Canterrain/bread-proof-monitor/proof_state.cpp

#include "proof_state.h"

#include <math.h>

#include "outcome_feedback.h"
#include "recipe_presets.h"

namespace {
constexpr int8_t kNoEventIndex = -1;
constexpr unsigned long kDistanceStaleAfterMs = 15000;
// A single noisy sample shouldn't permanently raise the floor: require the reading to stay
// above the current peak for a few consecutive ticks before it's trusted. This is short
// enough to accept genuine rise (which persists for many minutes, not seconds) but long
// enough to reject a one-off VL53L0X jitter spike, which reverts within a tick or two.
constexpr unsigned long kPeakConfirmMs = 8000;
// 8s is long enough to reject noise on a tall dough (a few mm of jitter is a small percentage of
// the height), but not on a very shallow one - Detroit Pizza's ~10mm-tall pan-pressed Final stage
// let ~2mm of ordinary jitter hold for a full 8s and lock in a false 15% peak (2026-09-29 live
// bake). Real rise is persistent (keeps climbing over minutes); noise is transient (reverts) -
// so a shallow dough needs a much longer hold before a candidate peak is trusted. This scales
// linearly between kPeakConfirmMs (at/above kTallConfirmReferenceHeightMm, unchanged from before)
// and kMaxPeakConfirmMs (at/below kShallowConfirmReferenceHeightMm) - see peakConfirmMs(). The
// exact numbers are a first-pass estimate from 2026-09-30 repeatability data (glass ~1mm spread
// vs. metal pans ~3mm spread on Set Empty captures, same order of magnitude as the phantom peak),
// not yet validated against a live shallow bake's actual noise *timing* - tune against the next
// one (see the pan-empty-calibration-test memory).
constexpr unsigned long kMaxPeakConfirmMs = 90000;
constexpr float kTallConfirmReferenceHeightMm = 60.0f;
constexpr float kShallowConfirmReferenceHeightMm = 15.0f;
// "Rise has slowed" message: the confirmed peak has to gain kStallMinGainPercent within
// kStallWindowMs, or the monitor says so - unless a fold or the target is already within
// kStallNearMilestonePercent (it is about to fire anyway). Measurement-based, not a timer: the
// window only measures how fast the dough is moving. First-guess numbers from the 2026-10-06
// no-knead bake (a cold-kitchen dough sat flat for about an hour with nothing to say so); tune
// against real runs.
constexpr unsigned long kStallWindowMs = 30UL * 60UL * 1000UL;
constexpr float kStallMinGainPercent = 2.0f;
constexpr float kStallNearMilestonePercent = 3.0f;
constexpr unsigned long kDefaultReferenceFloorSeconds = 20 * 60;
constexpr unsigned long kMinSegmentFloorSeconds = 8 * 60;
constexpr unsigned long kMaxSegmentFloorSeconds = 40 * 60;
// How long after Set Starting Dough Height, or after completing a fold, the rise is held steady
// (at 0% for a fresh start, at the already-earned percentage after a fold). Smoothing the surface and
// then watching it relax back up (or the mount shifting after being handled) moves the reading
// several mm in the first minutes, which would otherwise be counted - and permanently locked
// in by the peak - as real rise. Once the window ends, the settled reading becomes the start.
constexpr unsigned long kSettleWindowSeconds = 10 * 60;
// A fold or manual re-baseline only briefly disturbs a surface that's already mid-rise, unlike a
// fresh start where nothing has settled yet - real fold-to-fold gaps (King Arthur's own no-knead
// schedule runs ~15 minutes apart) leave little room for a full 10-minute hold on top of them.
constexpr unsigned long kPostDisturbanceSettleSeconds = 3 * 60;
// The peak only ever moves up, and this sensor jitters a few mm at the rig's standoff (about 1.4%
// of rise per mm on a 70mm dough), so symmetric noise alone turns into a one-sided climb in the
// peak within minutes. A new peak has to clear the old one by more than this to count.
constexpr float kPeakDeadbandMm = 3.0f;
// A fixed mm deadband is a small margin on a tall dough but can swallow most of a shallow
// container's whole target - 3mm was about 4% of a 70mm no-knead bucket but 8%+ of a ~36mm
// Detroit Pizza bulk container, against a 10% fold trigger. Capped here so a shallow container
// can't lose most of its own trigger range to noise margin; tall doughs are unaffected as long
// as the mm-based value stays under this.
constexpr float kMaxPeakDeadbandPercent = 4.0f;
constexpr float kReferenceTempF = 75.0f;
constexpr float kFermentationDoublingSpanF = 18.0f;

bool riseInputsReady(const AppState& state) {
  return proofHasEmptyCalibration(state) && proofHasStartingHeight(state) && state.smoothedDistanceMm > 0.0f;
}

bool loadSelectedPreset(const AppState& state, RecipePreset& preset) {
  return findRecipePreset(state.selectedRecipe, preset);
}

// The temperature that scaling decisions use: the slow-moving copy, not the raw air reading. Falls
// back to the raw reading until the smoothed copy has been seeded.
float scalingTemperature(const AppState& state) {
  return state.scalingTemperatureF > 0.0f ? state.scalingTemperatureF : state.temperatureF;
}

// The minimum time a segment must run before a fold/target crossing is trusted, scaled by
// measured temperature: warmer dough can legitimately move faster, colder dough should move
// slower, so an implausibly-fast reading is more suspicious in a cold kitchen, not less.
unsigned long requiredSegmentFloorSeconds(const AppState& state) {
  RecipePreset preset;
  const unsigned long referenceSeconds = loadSelectedPreset(state, preset)
                                              ? static_cast<unsigned long>(preset.referenceFloorMinutes) * 60UL
                                              : kDefaultReferenceFloorSeconds;

  if (!state.shtReady) return referenceSeconds;

  const float scale = powf(2.0f, (scalingTemperature(state) - kReferenceTempF) / kFermentationDoublingSpanF);
  if (scale <= 0.0f) return referenceSeconds;

  const unsigned long scaledSeconds = static_cast<unsigned long>(referenceSeconds / scale);
  if (scaledSeconds < kMinSegmentFloorSeconds) return kMinSegmentFloorSeconds;
  if (scaledSeconds > kMaxSegmentFloorSeconds) return kMaxSegmentFloorSeconds;
  return scaledSeconds;
}

// Published sourdough bulk-fermentation guidance ties the right rise target to dough
// temperature much more steeply than the confirm-window floor above does - roughly a halving
// every 6F around the same 75F reference, versus that floor's gentler 18F-doubling - because
// warm dough needs to be caught earlier to avoid overproofing, not just trusted sooner once
// crossed. Clamped to a 1.0-2.5x range: warmth can only LOWER a target or fold trigger, never raise
// it above its authored value. On a live no-knead bake (2026-10-06) a cooling kitchen kept pushing
// the first fold up from 18.5% to 21% while the dough barely moved, so the goalpost receded as
// fast as the dough advanced. A dough that has reached the authored rise has done what the recipe
// asked, however cold the room is. The cost is that a cold bulk is called at the 75F number,
// slightly earlier than published guidance for cool dough.
constexpr float kTargetDoublingSpanF = 6.0f;
constexpr float kMinTemperatureRiseScale = 1.0f;
constexpr float kMaxTemperatureRiseScale = 2.5f;

float temperatureRiseScale(const AppState& state) {
  if (!state.shtReady) return 1.0f;
  // Commercial-yeast recipes target a fixed rise ("until doubled") regardless of temperature -
  // only starter-leavened ones get this adjustment. See recipeUsesTemperatureScaledTarget().
  if (!recipeUsesTemperatureScaledTarget(state.selectedRecipe)) return 1.0f;

  float scale = powf(2.0f, (scalingTemperature(state) - kReferenceTempF) / kTargetDoublingSpanF);
  if (scale < kMinTemperatureRiseScale) scale = kMinTemperatureRiseScale;
  if (scale > kMaxTemperatureRiseScale) scale = kMaxTemperatureRiseScale;
  return scale;
}

// The live, temperature-adjusted version of state.targetRisePercent (itself the shipped or
// learned reference value) - what "done" actually means right now, not just at a 75F reference.
float liveTargetRisePercent(const AppState& state) {
  return state.targetRisePercent / temperatureRiseScale(state);
}

// Scales a fold's authored trigger by the same factor as the target above, so it stays at the
// same fraction of the way to target it was authored at (e.g. "a third of the way there"),
// just shifted to match tonight's actual temperature instead of the recipe's reference one.
float liveTriggerRisePercent(const AppState& state, uint8_t authoredTriggerPercent) {
  return static_cast<float>(authoredTriggerPercent) / temperatureRiseScale(state);
}

bool stageMatches(const FermentationEvent& event, const String& stage) {
  return event.stage != nullptr && stage == event.stage;
}

int8_t firstEventIndexForStage(const RecipePreset& preset, const String& stage) {
  for (uint8_t index = 0; index < preset.eventCount; ++index) {
    if (stageMatches(preset.events[index], stage)) return static_cast<int8_t>(index);
  }

  return kNoEventIndex;
}

int8_t nextEventIndexForStage(const RecipePreset& preset, const String& stage, int8_t currentIndex) {
  for (uint8_t index = static_cast<uint8_t>(currentIndex + 1); index < preset.eventCount; ++index) {
    if (stageMatches(preset.events[index], stage)) return static_cast<int8_t>(index);
  }

  return kNoEventIndex;
}

int8_t eventIndexFromCompletedCount(const RecipePreset& preset, const String& stage, uint8_t completedCount) {
  uint8_t seen = 0;

  for (uint8_t index = 0; index < preset.eventCount; ++index) {
    if (!stageMatches(preset.events[index], stage)) continue;
    if (seen == completedCount) return static_cast<int8_t>(index);
    ++seen;
  }

  return kNoEventIndex;
}

float doughHeightFromDistanceMm(const AppState& state, float distanceMm) {
  if (!proofHasEmptyCalibration(state) || distanceMm <= 0.0f) return 0.0f;
  return state.emptyDistanceMm - distanceMm;
}

float risePercentFromDistances(const AppState& state, float baselineDistanceMm, float currentDistanceMm) {
  const float baselineHeight = doughHeightFromDistanceMm(state, baselineDistanceMm);
  const float currentHeight = doughHeightFromDistanceMm(state, currentDistanceMm);

  if (baselineHeight <= 0.0f || currentHeight <= 0.0f) return 0.0f;

  const float risePercent = ((currentHeight - baselineHeight) / baselineHeight) * 100.0f;
  return risePercent > 0.0f ? risePercent : 0.0f;
}

int8_t resolvedPendingEventIndex(const AppState& state, const RecipePreset& preset) {
  if (state.pendingEventIndex >= 0 &&
      state.pendingEventIndex < static_cast<int8_t>(preset.eventCount) &&
      stageMatches(preset.events[state.pendingEventIndex], state.selectedStage)) {
    return state.pendingEventIndex;
  }

  return eventIndexFromCompletedCount(preset, state.selectedStage, state.completedEventCount);
}

void primeEventStateForSelection(AppState& state, const RecipePreset* preset = nullptr) {
  // A proof that's already Running/TargetReached has a live segment clock and real banked
  // progress - there's nothing here that's safe to re-prime out from under it. Zeroing
  // segmentStartedAtMillis while Running is what let simply re-applying the same profile/target
  // (e.g. the picker's Apply button, even with nothing changed) permanently freeze the settle
  // window: currentSegmentElapsedSeconds() treats 0 as "never started" and nothing else re-arms
  // it outside of starting a proof, completing a fold, or a settle-release. startProof() and
  // beginFinalStage() only ever call this while proofState is NotStarted anyway (either already,
  // or via clearActiveProofRunForStage() just above), so this guard doesn't change their behavior.
  if (state.proofState == ProofState::Running || state.proofState == ProofState::TargetReached) return;

  state.pendingEventActive = false;
  state.completedEventCount = 0;
  state.pendingEventNotified = false;
  state.segmentBaselineDistanceMm = 0.0f;
  state.completedProgressOffsetPercent = 0.0f;
  state.peakProgressPercent = 0.0f;
  state.peakCandidateSinceMillis = 0;
  state.pendingEventIndex = kNoEventIndex;
  state.segmentStartedAtMillis = 0;
  state.segmentElapsedOffsetSeconds = 0;

  if (preset != nullptr) {
    state.pendingEventIndex = firstEventIndexForStage(*preset, state.selectedStage);
  }
}

bool canPrepareFinalProof(const AppState& state, RecipePreset& preset) {
  return state.recipeConfigured &&
         state.selectedStage == "Bulk" &&
         findRecipePreset(state.selectedRecipe, preset) &&
         preset.hasFinal;
}

void clearActiveProofRun(AppState& state) {
  state.startDistanceMm = 0.0f;
  state.segmentBaselineDistanceMm = 0.0f;
  state.completedProgressOffsetPercent = 0.0f;
  state.peakProgressPercent = 0.0f;
  state.peakCandidateSinceMillis = 0;
  state.proofStartedAtMillis = 0;
  state.elapsedOffsetSeconds = 0;
  state.finalElapsedSeconds = 0;
  state.finalRisePercent = 0.0f;
  state.resumeIgnoreUntil = 0;
  state.targetNotified = false;
  state.pendingEventActive = false;
  state.pendingEventNotified = false;
  state.settlingActive = false;
  state.stallRefMillis = 0;
  state.proofState = ProofState::NotStarted;
}

String nextMilestoneText(const AppState& state) {
  // Checked before the fold preview below: Start New Proof re-primes pendingEventIndex to the
  // previous recipe's first fold before recipeConfigured is cleared, which would otherwise
  // preview a stale fold from a proof that hasn't been chosen again yet.
  if (!state.recipeConfigured) return "Choose your bake, then set empty setup and starting dough height.";

  const ActiveFermentationEventStatus eventStatus = currentFermentationEvent(state);
  if (eventStatus.exists && !eventStatus.due) {
    return String("Next: ") + eventStatus.event.title + " at " +
           String(liveTriggerRisePercent(state, eventStatus.event.triggerRisePercent), 0) + "%";
  }

  if (state.selectedStage == "Bulk") {
    return String("Next: Ready to Shape at ") + String(liveTargetRisePercent(state), 0) + "%";
  }

  return String("Next: Ready to Bake at ") + String(liveTargetRisePercent(state), 0) + "%";
}
}  // namespace

// Progress against this tick's fresh, unsmoothed reading rather than smoothedDistanceMm. Used
// only for peak-candidate confirmation below: the EMA blend in readSensors() can keep a single
// bad tick visibly elevated for tens of seconds while it decays back out, which is long enough
// to satisfy the 8-second confirm window on its own. Each tick's median-of-5 read is independent
// of the others, so a transient error here reverts on the very next tick instead of smearing
// across several. Exposed via the header for /data's diagnostic fields as well.
float instantRawProgressPercent(const AppState& state) {
  if (!proofHasStartingHeight(state)) return 0.0f;

  const float baselineDistanceMm = state.segmentBaselineDistanceMm > 0.0f
                                       ? state.segmentBaselineDistanceMm
                                       : state.startDistanceMm;
  const float segmentRise = risePercentFromDistances(state, baselineDistanceMm, state.lastRawDistanceMm);
  return state.completedProgressOffsetPercent + segmentRise;
}

// kPeakDeadbandMm expressed as percent of rise for this segment's own baseline height. Exposed
// via the header for /data's diagnostic fields as well.
float peakDeadbandPercent(const AppState& state) {
  const float baselineDistanceMm = state.segmentBaselineDistanceMm > 0.0f
                                       ? state.segmentBaselineDistanceMm
                                       : state.startDistanceMm;
  const float baselineHeight = doughHeightFromDistanceMm(state, baselineDistanceMm);
  if (baselineHeight <= 0.0f) return 0.0f;

  const float deadbandPercent = (kPeakDeadbandMm / baselineHeight) * 100.0f;
  return deadbandPercent < kMaxPeakDeadbandPercent ? deadbandPercent : kMaxPeakDeadbandPercent;
}

// How long a candidate peak has to hold above the deadband before it's trusted - see
// kMaxPeakConfirmMs above for why this scales with how shallow the dough is. Exposed via the
// header for /data's diagnostic fields as well.
unsigned long peakConfirmMs(const AppState& state) {
  const float baselineDistanceMm = state.segmentBaselineDistanceMm > 0.0f
                                       ? state.segmentBaselineDistanceMm
                                       : state.startDistanceMm;
  const float baselineHeight = doughHeightFromDistanceMm(state, baselineDistanceMm);
  if (baselineHeight <= 0.0f || baselineHeight >= kTallConfirmReferenceHeightMm) return kPeakConfirmMs;
  if (baselineHeight <= kShallowConfirmReferenceHeightMm) return kMaxPeakConfirmMs;

  const float t = (kTallConfirmReferenceHeightMm - baselineHeight) /
                   (kTallConfirmReferenceHeightMm - kShallowConfirmReferenceHeightMm);
  return kPeakConfirmMs + static_cast<unsigned long>(t * (kMaxPeakConfirmMs - kPeakConfirmMs));
}

// True when the confirmed peak hasn't gained kStallMinGainPercent in kStallWindowMs and neither
// the next fold nor the target is within kStallNearMilestonePercent. Only while actively running:
// not while settling, waiting on a fold, paused, finished, or already at target.
bool riseStalled(const AppState& state) {
  if (state.proofState != ProofState::Running) return false;
  if (state.settlingActive || state.pendingEventActive || state.stallRefMillis == 0) return false;
  if (!riseInputsReady(state) || proofDistanceReadingStale(state)) return false;
  if (millis() - state.stallRefMillis < kStallWindowMs) return false;

  float nextMilestone = liveTargetRisePercent(state);
  const ActiveFermentationEventStatus eventStatus = currentFermentationEvent(state);
  if (eventStatus.exists) {
    nextMilestone = liveTriggerRisePercent(state, eventStatus.event.triggerRisePercent);
  }
  return (nextMilestone - state.peakProgressPercent) > kStallNearMilestonePercent;
}

bool proofHasEmptyCalibration(const AppState& state) {
  return state.emptyDistanceMm > 0.0f;
}

bool proofHasStartingHeight(const AppState& state) {
  return state.startDistanceMm > 0.0f;
}

bool proofDistanceReadingStale(const AppState& state) {
  if (!state.loxReady) return true;
  if (state.smoothedDistanceMm <= 0.0f) return true;
  if (state.lastValidDistanceAtMillis == 0) return true;
  return millis() - state.lastValidDistanceAtMillis > kDistanceStaleAfterMs;
}

bool proofCanSetEmpty(const AppState& state) {
  return state.proofState != ProofState::Paused && state.proofState != ProofState::Finished;
}

bool proofCanSetStart(const AppState& state) {
  return proofHasEmptyCalibration(state) &&
         state.proofState != ProofState::Paused &&
         state.proofState != ProofState::Finished;
}

bool proofCanPause(const AppState& state) {
  return state.proofState == ProofState::Running || state.proofState == ProofState::TargetReached;
}

bool proofCanResume(const AppState& state) {
  return state.proofState == ProofState::Paused;
}

bool proofCanFinish(const AppState& state) {
  return proofHasStartingHeight(state) && state.proofState != ProofState::Finished;
}

bool proofCanCompleteEvent(const AppState& state) {
  const ActiveFermentationEventStatus eventStatus = currentFermentationEvent(state);
  return eventStatus.exists &&
         eventStatus.due &&
         state.proofState != ProofState::Paused &&
         state.proofState != ProofState::Finished &&
         !proofDistanceReadingStale(state);
}

bool proofCanRebaseline(const AppState& state) {
  return proofHasStartingHeight(state) &&
         state.proofState != ProofState::Paused &&
         state.proofState != ProofState::Finished &&
         !proofDistanceReadingStale(state);
}

float displayedTargetRisePercent(const AppState& state) {
  return liveTargetRisePercent(state);
}

bool proofAwaitingDoughPrep(const AppState& state) {
  return state.recipeConfigured &&
         state.proofState != ProofState::Finished &&
         !proofDistanceReadingStale(state) &&
         proofHasEmptyCalibration(state) &&
         !proofHasStartingHeight(state);
}

float currentDoughHeightMm(const AppState& state) {
  if (!proofHasEmptyCalibration(state) || state.smoothedDistanceMm <= 0.0f) return 0.0f;
  return state.emptyDistanceMm - state.smoothedDistanceMm;
}

float startingDoughHeightMm(const AppState& state) {
  if (!proofHasEmptyCalibration(state) || !proofHasStartingHeight(state)) return 0.0f;
  return state.emptyDistanceMm - state.startDistanceMm;
}

float liveRisePercent(const AppState& state) {
  const float startHeight = startingDoughHeightMm(state);
  const float currentHeight = currentDoughHeightMm(state);

  if (startHeight <= 0.0f || currentHeight <= 0.0f) return 0.0f;
  return ((currentHeight - startHeight) / startHeight) * 100.0f;
}

// What's shown and reasoned about everywhere but the confirmation logic itself: the confirmed
// peak, not the live raw reading. The peak only moves once a rise clears the deadband and holds
// for the confirm window, so this can't jump around on noise the way showing the raw reading
// directly would - it only changes when something's actually been confirmed.
float overallProgressPercent(const AppState& state) {
  return state.peakProgressPercent;
}

float displayRisePercent(const AppState& state) {
  if (state.proofState == ProofState::Finished) return state.finalRisePercent;
  return overallProgressPercent(state);
}

unsigned long currentElapsedSeconds(const AppState& state) {
  switch (state.proofState) {
    case ProofState::Running:
    case ProofState::TargetReached:
      if (state.proofStartedAtMillis == 0) return state.elapsedOffsetSeconds;
      return state.elapsedOffsetSeconds + ((millis() - state.proofStartedAtMillis) / 1000);
    case ProofState::Paused:
      return state.elapsedOffsetSeconds;
    case ProofState::Finished:
      return state.finalElapsedSeconds;
    case ProofState::NotStarted:
    default:
      return 0;
  }
}

unsigned long currentSegmentElapsedSeconds(const AppState& state) {
  switch (state.proofState) {
    case ProofState::Running:
    case ProofState::TargetReached:
      if (state.segmentStartedAtMillis == 0) return state.segmentElapsedOffsetSeconds;
      return state.segmentElapsedOffsetSeconds + ((millis() - state.segmentStartedAtMillis) / 1000);
    case ProofState::Paused:
      return state.segmentElapsedOffsetSeconds;
    case ProofState::Finished:
    case ProofState::NotStarted:
    default:
      return 0;
  }
}

String elapsedText(const AppState& state) {
  if (!proofHasStartingHeight(state) && state.proofState == ProofState::NotStarted) return "Not started";

  const unsigned long elapsedSeconds = currentElapsedSeconds(state);
  const int hours = elapsedSeconds / 3600;
  const int minutes = (elapsedSeconds % 3600) / 60;
  return String(hours) + "h " + String(minutes) + "m";
}

String proofStateApiValue(ProofState state) {
  switch (state) {
    case ProofState::Running:
      return "running";
    case ProofState::Paused:
      return "paused";
    case ProofState::TargetReached:
      return "target-reached";
    case ProofState::Finished:
      return "finished";
    case ProofState::NotStarted:
    default:
      return "not-started";
  }
}

String statusText(const AppState& state) {
  if (state.proofState == ProofState::Finished) return "Proof finished";
  if (state.proofState == ProofState::Paused) return "Paused";

  if (!state.loxReady && !state.shtReady) return "Sensors not found";
  if (!state.loxReady) return "Distance sensor not found";
  if (!state.shtReady) return "Temperature sensor not found";
  if (proofDistanceReadingStale(state)) {
    return state.pendingEventActive ? "Settling after fold" : "Distance reading unstable";
  }
  if (!state.recipeConfigured) return "Choose Your Bake";
  if (state.awaitingFinalProofStart) return "Bulk proof complete";
  if (!proofHasEmptyCalibration(state)) return "Set empty setup";
  if (!proofHasStartingHeight(state)) return "Set starting dough height";
  if (state.settlingActive) return "Settling";
  const ActiveFermentationEventStatus eventStatus = currentFermentationEvent(state);
  if (eventStatus.exists && eventStatus.due) return eventStatus.event.title;
  if (state.proofState == ProofState::TargetReached) return "Target reached";

  const float rise = overallProgressPercent(state);
  const float liveTarget = liveTargetRisePercent(state);
  if (rise >= liveTarget) return "Confirming target reached";
  if (riseStalled(state)) return "Rise has slowed";
  if (rise < 10.0f) return "Just getting started";
  if (rise < liveTarget * 0.75f) return "Rising";
  return "Getting close";
}

String nextStepText(const AppState& state) {
  if (state.proofState != ProofState::TargetReached) return "";

  // "Bubbles along the side" is a bulk-fermentation-in-a-container cue, which fits every
  // Bulk stage here (that's always monitored in some straight-sided vessel). Final proof is
  // almost always shaped dough in a pan, tray, or sheet instead, viewed from above, so it gets
  // its own wording rather than reusing a container-specific check that wouldn't apply.
  String checks = "slight jiggle, slow springback from a gentle poke, ";
  if (state.selectedStage == "Final") {
    checks += "and a visibly puffy, rounded top";
  } else {
    // A recipe-specific extra (e.g. stretching thin without tearing) joins the list; the
    // "and" moves to the end so the sentence still reads naturally.
    RecipePreset preset;
    if (loadSelectedPreset(state, preset) && preset.bulkReadinessCheck != nullptr) {
      checks += "visible bubbles along the side, and " + String(preset.bulkReadinessCheck);
    } else {
      checks += "and visible bubbles along the side";
    }
  }

  // At target the app keeps tracking and only Finish Proof ends it - there is no Resume button
  // here (that exists only while paused), so "needs more time" means leave it running.
  return "Check for " + checks + ". If it looks right, finish this proof. If it needs more time, "
         "just leave it running. Tracking continues until you press Finish Proof.";
}

String phoneAlertText(const AppState& state) {
  if (state.pendingEventActive) {
    return state.pendingEventNotified ? "Alert sent" : "Alert ready";
  }

  return state.targetNotified ? "Alert sent" : "Alert ready";
}

String currentStepTitle(const AppState& state) {
  if (!state.recipeConfigured) return "Choose Your Bake";
  if (state.awaitingFinalProofStart) return "Bulk proof complete";
  if (!proofHasEmptyCalibration(state)) return "Set empty setup";
  if (!proofHasStartingHeight(state)) return "Set starting dough height";
  if (state.proofState == ProofState::Paused) return "Monitoring paused";
  const ActiveFermentationEventStatus eventStatus = currentFermentationEvent(state);
  if (eventStatus.exists && eventStatus.due) return eventStatus.event.title;
  if (state.proofState == ProofState::TargetReached) return "Target reached";
  if (state.proofState == ProofState::Finished) return "Proof finished";
  return "Monitor proof";
}

String currentStepInstruction(const AppState& state) {
  // Checked before the "choose a bake" branch below: a just-finished proof clears
  // recipeConfigured so Current Step reads "Choose Your Bake" again, but the dough from
  // that finished proof may still need a physical next step (shape, refrigerate, bake). Show
  // that instead of jumping straight to "choose a bake" and losing it.
  if (state.proofState == ProofState::Finished) {
    RecipePreset preset;
    if (loadSelectedPreset(state, preset) && preset.untrackedFinalNote != nullptr) {
      return String(preset.untrackedFinalNote);
    }
    return "This proof is complete. Start a new proof when you are ready to monitor another batch.";
  }

  if (!state.recipeConfigured) {
    return "Choose your bake or adjust a custom target before you start monitoring.";
  }

  if (proofDistanceReadingStale(state)) {
    if (state.pendingEventActive) {
      return "Give the reading a few seconds to settle now that the lid is back on. Complete Step "
             "will become available once it does, no action needed.";
    }
    return "Distance readings look stale or unstable right now. Check sensor position and lid placement, then wait for live readings to settle.";
  }

  if (!proofHasEmptyCalibration(state)) {
    if (state.awaitingFinalProofStart || state.selectedStage == "Final") {
      return "Place the empty final-proof setup under the sensor, then press Set Empty Setup.";
    }
    return "Place the empty proof setup under the sensor, then press Set Empty Setup.";
  }

  if (state.awaitingFinalProofStart) {
    RecipePreset finalPreset;
    if (loadSelectedPreset(state, finalPreset) && finalPreset.sourceUrl != nullptr) {
      return "Bulk proof complete. Follow the linked recipe to shape your dough, then place "
             "the monitor over it and press Set Starting Dough Height to begin final proof.";
    }
    return "Bulk proof complete. Shape your dough, place the monitor over the shaped dough, then press Set Starting Dough Height to begin final proof.";
  }

  if (!proofHasStartingHeight(state)) {
    RecipePreset preset;
    const bool hasPreset = loadSelectedPreset(state, preset);
    const bool hasRecipe = hasPreset && preset.sourceUrl != nullptr;

    if (state.selectedStage == "Final") {
      if (hasRecipe) {
        return "Follow the linked recipe to shape your dough, then place the monitor over "
               "it, let it settle for a moment, and press Set Starting Dough Height.";
      }
      return "Place the monitor over the shaped dough, let it settle for a moment, then "
             "press Set Starting Dough Height.";
    }

    if (hasPreset && preset.premixNote != nullptr) {
      return String(preset.premixNote) +
             " Then, for bulk rise, place the dough in the proof container, smooth the "
             "top, let the lid settle for a moment, and press Set Starting Dough Height.";
    }

    if (hasRecipe) {
      return "Follow the linked recipe to mix and shape your dough, then place it in the "
             "proof container, smooth the top, let the lid settle for a moment, and press "
             "Set Starting Dough Height.";
    }

    return "Place the dough in the proof container, smooth the top, let the lid settle "
           "for a moment, then press Set Starting Dough Height.";
  }

  if (state.proofState == ProofState::Paused) {
    return "Resume monitoring when the dough is back in place and you want the proof timer to continue.";
  }

  const ActiveFermentationEventStatus eventStatus = currentFermentationEvent(state);
  if (eventStatus.exists && eventStatus.due) {
    return "Pause Monitoring before you remove the lid. " + String(eventStatus.event.instruction) +
           " Resume Monitoring once the lid is back on. Complete Step won't be "
           "available until you do.";
  }

  if (state.proofState == ProofState::TargetReached) {
    return nextStepText(state);
  }

  if (overallProgressPercent(state) >= liveTargetRisePercent(state)) {
    return "The reading has confirmed your target already, but the app waits until enough "
           "time has passed at this temperature before finishing, so an unrealistically fast "
           "measurement isn't trusted on its own. No action needed, this resolves on its own "
           "shortly.";
  }

  if (riseStalled(state)) {
    return "The rise has gained less than 2 points in the last 30 minutes and is still short of "
           "the next step. That can be normal in a cool room or an early slow phase. Check the "
           "dough: if it still looks puffy and active, keep waiting. If it looks flat or "
           "sluggish, it may need a warmer spot or more time. The monitor keeps tracking either "
           "way.";
  }

  return "Keep monitoring until the dough reaches the selected target rise.";
}

String upcomingStepText(const AppState& state) {
  // recipeConfigured is checked first so a just-finished proof (which clears it) surfaces
  // "choose your bake" here as the real next step, alongside the Choose Your Bake button.
  // The Bulk-to-Final continuation keeps recipeConfigured true throughout, so it still falls
  // through to the Finished check below and shows no stale next-step text.
  if (!state.recipeConfigured) return nextMilestoneText(state);
  if (state.proofState == ProofState::Finished) return "";
  if (proofDistanceReadingStale(state)) {
    return state.pendingEventActive ? "Wait a few seconds, then press Complete Step."
                                     : "Wait for stable live distance readings.";
  }
  if (!proofHasEmptyCalibration(state)) return "Set starting dough height.";
  if (state.awaitingFinalProofStart) return String("Next: Ready to Bake at ") + String(liveTargetRisePercent(state), 0) + "%";
  if (!proofHasStartingHeight(state)) return nextMilestoneText(state);
  const ActiveFermentationEventStatus eventStatus = currentFermentationEvent(state);
  if (eventStatus.exists && eventStatus.due) {
    RecipePreset preset;
    if (loadSelectedPreset(state, preset)) {
      const int8_t nextIndex = nextEventIndexForStage(preset, state.selectedStage, eventStatus.index);
      if (nextIndex >= 0) {
        return String("Next: ") + preset.events[nextIndex].title + " at " +
               String(liveTriggerRisePercent(state, preset.events[nextIndex].triggerRisePercent), 0) + "%";
      }
    }
    return state.selectedStage == "Bulk"
               ? String("Next: Ready to Shape at ") + String(liveTargetRisePercent(state), 0) + "%"
               : String("Next: Ready to Bake at ") + String(liveTargetRisePercent(state), 0) + "%";
  }
  if (state.proofState == ProofState::TargetReached) return "Finish Proof when the dough looks ready.";
  return nextMilestoneText(state);
}

ActiveFermentationEventStatus currentFermentationEvent(const AppState& state) {
  ActiveFermentationEventStatus status;
  RecipePreset preset;
  if (!loadSelectedPreset(state, preset)) return status;

  const int8_t eventIndex = resolvedPendingEventIndex(state, preset);
  if (eventIndex < 0) return status;

  status.exists = true;
  status.index = eventIndex;
  status.notified = state.pendingEventNotified;
  status.event = preset.events[eventIndex];
  // Use the debounced peak here, not overallProgressPercent() (which is max(raw, peak)) -
  // a fold must go through the same 8-second confirm window as a target-reached decision
  // does, or a single noisy sample can mark it due and fire a phone alert with no confirmation
  // at all, even though the peak itself never actually moved.
  const bool crossedTrigger = proofHasEmptyCalibration(state) &&
                              proofHasStartingHeight(state) &&
                              !state.awaitingFinalProofStart &&
                              state.proofState != ProofState::Finished &&
                              currentSegmentElapsedSeconds(state) >= requiredSegmentFloorSeconds(state) &&
                              state.peakProgressPercent >= liveTriggerRisePercent(state, status.event.triggerRisePercent);
  status.due = state.pendingEventActive || crossedTrigger;
  return status;
}

void clearActiveProofRunForStage(AppState& state, bool clearEmptyCalibration) {
  clearActiveProofRun(state);
  if (clearEmptyCalibration) {
    state.emptyDistanceMm = 0.0f;
  }
}

bool stageChangeNeedsEmptyReset(const String& previousProfile,
                                const String& previousStage,
                                const String& nextProfile,
                                const String& nextStage) {
  // A different recipe should never inherit a leftover run's state, even if both happen to
  // default to the same stage name (e.g. "Bulk" to "Bulk") - that's a different container
  // and a different bake, not a continuation of the old one.
  if (previousProfile != nextProfile) return true;
  if (previousStage == nextStage) return false;
  return profileRequiresStageSetupReset(previousProfile) || profileRequiresStageSetupReset(nextProfile);
}

void resetFermentationEventState(AppState& state) {
  RecipePreset preset;
  if (loadSelectedPreset(state, preset)) {
    primeEventStateForSelection(state, &preset);
  } else {
    primeEventStateForSelection(state, nullptr);
  }
}

void completeCurrentEvent(AppState& state) {
  const ActiveFermentationEventStatus eventStatus = currentFermentationEvent(state);
  if (!eventStatus.exists || !eventStatus.due || state.smoothedDistanceMm <= 0.0f) return;

  RecipePreset preset;
  if (!loadSelectedPreset(state, preset)) return;

  // Use the already-latched peak, not a fresh recompute: captureStableDistanceMm() has
  // already overwritten smoothedDistanceMm with the post-fold reading, so comparing it
  // against the still-stale pre-fold segmentBaselineDistanceMm here would mix
  // measurements from before and after the physical disturbance.
  state.completedProgressOffsetPercent = state.peakProgressPercent;
  state.segmentBaselineDistanceMm = state.smoothedDistanceMm;
  state.peakCandidateSinceMillis = 0;
  state.pendingEventActive = false;
  state.completedEventCount += 1;
  state.pendingEventNotified = false;
  state.pendingEventIndex = nextEventIndexForStage(preset, state.selectedStage, eventStatus.index);
  state.targetNotified = false;
  state.segmentStartedAtMillis = millis();
  state.segmentElapsedOffsetSeconds = 0;
  // Folded dough relaxes back up just like smoothed dough does, so hold the earned percentage
  // (the offset above) steady until it settles rather than counting that as new rise.
  state.settlingActive = true;
  state.settlingIsPostDisturbance = true;
  updateProofStateFromRise(state);
}

void rebaselineProof(AppState& state) {
  if (!proofCanRebaseline(state) || state.smoothedDistanceMm <= 0.0f) return;

  // Same reasoning as completeCurrentEvent(): use the already-latched peak rather than
  // recomputing against the freshly-captured (post-disturbance) distance.
  state.completedProgressOffsetPercent = state.peakProgressPercent;
  state.segmentBaselineDistanceMm = state.smoothedDistanceMm;
  state.peakCandidateSinceMillis = 0;
  state.segmentStartedAtMillis = millis();
  state.segmentElapsedOffsetSeconds = 0;
  // Lid-off handling is the same kind of brief disturbance a fold is - hold steady and let it
  // settle before trusting the reading again, same as completeCurrentEvent().
  state.settlingActive = true;
  state.settlingIsPostDisturbance = true;
  updateProofStateFromRise(state);
}

void startProof(AppState& state) {
  RecipePreset preset;
  const RecipePreset* presetPtr = loadSelectedPreset(state, preset) ? &preset : nullptr;
  primeEventStateForSelection(state, presetPtr);
  state.startDistanceMm = state.smoothedDistanceMm;
  state.segmentBaselineDistanceMm = state.smoothedDistanceMm;
  state.peakProgressPercent = 0.0f;
  state.proofStartedAtMillis = millis();
  state.elapsedOffsetSeconds = 0;
  state.finalElapsedSeconds = 0;
  state.finalRisePercent = 0.0f;
  state.targetNotified = false;
  state.awaitingFinalProofStart = false;
  state.segmentStartedAtMillis = millis();
  state.segmentElapsedOffsetSeconds = 0;
  state.settlingActive = true;
  state.settlingIsPostDisturbance = false;
  state.proofState = ProofState::Running;
}

void pauseProof(AppState& state) {
  if (!proofCanPause(state)) return;

  state.elapsedOffsetSeconds = currentElapsedSeconds(state);
  state.proofStartedAtMillis = 0;
  state.segmentElapsedOffsetSeconds = currentSegmentElapsedSeconds(state);
  state.segmentStartedAtMillis = 0;
  state.proofState = ProofState::Paused;
}

void resumeProof(AppState& state) {
  if (!proofCanResume(state)) return;

  state.proofStartedAtMillis = millis();
  state.segmentStartedAtMillis = millis();
  state.resumeIgnoreUntil = millis() + 6000;
  // Paused time shouldn't count toward a stall.
  state.stallRefMillis = 0;
  state.proofState = ProofState::Running;
  updateProofStateFromRise(state);
}

void queuePendingOutcome(AppState& state, const String& recipe, const String& stage) {
  if (!state.outcomeFeedbackPending) {
    state.outcomeFeedbackPending = true;
    state.outcomeRecipe = recipe;
    state.outcomeStage = stage;
    return;
  }

  // Something's already waiting to be rated (e.g. a Bulk rating from earlier in this same
  // proof) - hold this one rather than clobbering it, and promote it once the current one is
  // answered. See handleRateOutcome() in web_dashboard.cpp.
  state.outcomeFeedbackPendingNext = true;
  state.outcomeRecipeNext = recipe;
  state.outcomeStageNext = stage;
}

void advanceOutcomeQueue(AppState& state) {
  if (state.outcomeFeedbackPendingNext) {
    state.outcomeFeedbackPending = true;
    state.outcomeRecipe = state.outcomeRecipeNext;
    state.outcomeStage = state.outcomeStageNext;
    state.outcomeFeedbackPendingNext = false;
    state.outcomeRecipeNext = "";
    state.outcomeStageNext = "";
  } else {
    state.outcomeFeedbackPending = false;
    state.outcomeRecipe = "";
    state.outcomeStage = "";
  }
}

void clearAllPendingOutcomes(AppState& state) {
  state.outcomeFeedbackPending = false;
  state.outcomeRecipe = "";
  state.outcomeStage = "";
  state.outcomeFeedbackPendingNext = false;
  state.outcomeRecipeNext = "";
  state.outcomeStageNext = "";
}

void finishProof(AppState& state) {
  if (!proofCanFinish(state)) return;

  state.finalElapsedSeconds = currentElapsedSeconds(state);
  state.proofStartedAtMillis = 0;
  state.elapsedOffsetSeconds = state.finalElapsedSeconds;
  state.finalRisePercent = overallProgressPercent(state);
  state.awaitingFinalProofStart = false;
  state.proofState = ProofState::Finished;

  RecipePreset preset;
  if (!canPrepareFinalProof(state, preset)) {
    queuePendingOutcome(state, state.selectedRecipe, state.selectedStage);
    // Nothing further to monitor for this recipe. Drop back to "no proof selected" so the
    // next bake starts from Choose Your Bake rather than stranding the user on a stale
    // finished screen for the recipe they just baked.
    state.recipeConfigured = false;
    return;
  }

  // Bulk is done and we're about to auto-start Final - queue a rating for the Bulk stage now,
  // rather than only ever asking about whichever stage finishes last. Otherwise Bulk targets
  // for two-stage recipes could never learn from feedback at all.
  queuePendingOutcome(state, state.selectedRecipe, state.selectedStage);

  state.selectedStage = "Final";
  state.targetRisePercent = adjustedTarget(preset.name, "Final", preset.final);
  clearActiveProofRunForStage(state, profileRequiresStageSetupReset(state.selectedRecipe));
  primeEventStateForSelection(state, &preset);
  state.awaitingFinalProofStart = true;
}

void startNewProof(AppState& state) {
  clearActiveProofRunForStage(state, false);
  resetFermentationEventState(state);
  state.awaitingFinalProofStart = false;
  // Back to "no proof selected" so Choose Your Bake is the prominent next step, even
  // though the recipe, stage, and target stay put underneath so the picker still opens
  // pre-filled with what was just used.
  state.recipeConfigured = false;
  // A rating for a run you're no longer looking at isn't useful feedback, and the recipe/stage
  // it would have nudged gets another chance from whatever's baked next.
  clearAllPendingOutcomes(state);
}

void updateProofStateFromRise(AppState& state) {
  if (state.proofState != ProofState::Running && state.proofState != ProofState::TargetReached) return;
  if (!riseInputsReady(state)) return;
  if (proofDistanceReadingStale(state)) return;

  if (state.settlingActive) {
    const unsigned long settleWindowSeconds =
        state.settlingIsPostDisturbance ? kPostDisturbanceSettleSeconds : kSettleWindowSeconds;
    if (currentSegmentElapsedSeconds(state) < settleWindowSeconds) {
      // Nothing counts yet - no peak, no fold, no target, and the stall window starts fresh once
      // the hold ends.
      state.pendingEventActive = false;
      state.stallRefMillis = 0;
      state.proofState = ProofState::Running;
      return;
    }
    // Window's over: whatever the surface settled to is the real starting point. The proof's own
    // starting height only moves if this was the initial window - after a fold it stays put.
    if (state.completedProgressOffsetPercent <= 0.0f) {
      state.startDistanceMm = state.smoothedDistanceMm;
    }
    state.segmentBaselineDistanceMm = state.smoothedDistanceMm;
    state.peakProgressPercent = state.completedProgressOffsetPercent;
    state.peakCandidateSinceMillis = 0;
    state.settlingActive = false;
    return;
  }

  // Confirmation is checked against this tick's own instant reading, not the smoothed display
  // value - see instantRawProgressPercent() for why.
  const float instantProgress = instantRawProgressPercent(state);
  const float deadbandPercent = peakDeadbandPercent(state);
  if (state.pendingEventActive) {
    // A fold is waiting on the baker. The peak freezes at whatever fired the alert: once the
    // dough is lifted and folded its surface sits at a different height, and Complete Step copies
    // the peak into the offset, so anything the peak banked between Resume and Complete Step
    // would be the fold's own reshaping counted as rise. (Costs the few points of real rise
    // between the alert and the fold.)
    state.peakCandidateSinceMillis = 0;
  } else if (instantProgress > state.peakProgressPercent + deadbandPercent) {
    if (state.peakCandidateSinceMillis == 0) {
      state.peakCandidateSinceMillis = millis();
    } else if (millis() - state.peakCandidateSinceMillis >= peakConfirmMs(state)) {
      // Lands one deadband under the reading, so whatever noise helped it clear the old peak
      // doesn't stay banked. Decisions run at most about a deadband behind real progress.
      state.peakProgressPercent = instantProgress - deadbandPercent;
    }
  } else {
    state.peakCandidateSinceMillis = 0;
  }

  // Stall tracking for the "rise has slowed" message: restart the window whenever the confirmed
  // peak gains kStallMinGainPercent. While a fold is pending the peak is frozen on purpose, so
  // that isn't a stall - hold the reference unset until the fold is done.
  if (state.pendingEventActive) {
    state.stallRefMillis = 0;
  } else if (state.stallRefMillis == 0 ||
             state.peakProgressPercent >= state.stallRefPeakPercent + kStallMinGainPercent) {
    state.stallRefPeakPercent = state.peakProgressPercent;
    state.stallRefMillis = millis();
  }

  const ActiveFermentationEventStatus eventStatus = currentFermentationEvent(state);
  if (eventStatus.exists && eventStatus.due) {
    state.pendingEventActive = true;
    state.proofState = ProofState::Running;
    return;
  }

  state.pendingEventActive = false;
  if (currentSegmentElapsedSeconds(state) >= requiredSegmentFloorSeconds(state) &&
      state.peakProgressPercent >= liveTargetRisePercent(state)) {
    state.proofState = ProofState::TargetReached;
    return;
  }

  state.proofState = ProofState::Running;
}
